squishy-scsi/squishy/docs/mascot.md

# Mascot - Sachi

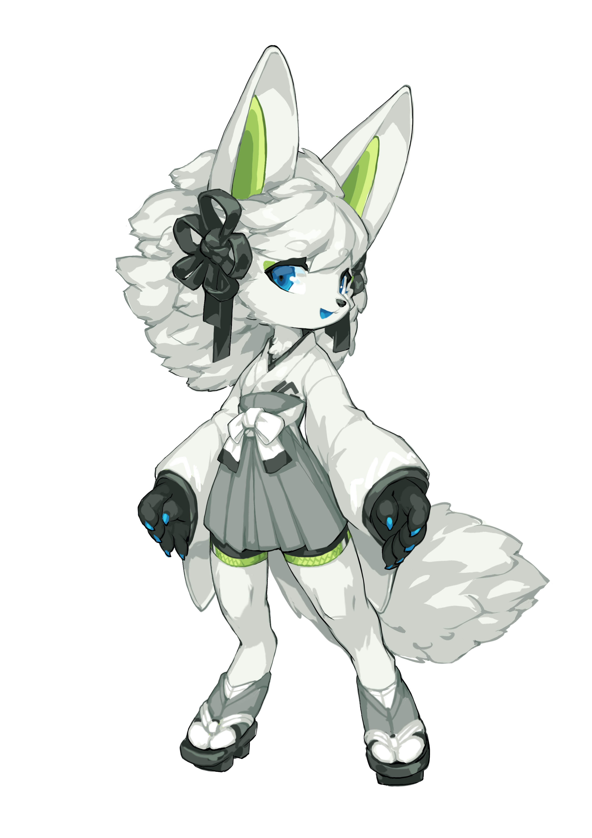
[picture p3: contrib/img/sachi/electrichearts_20211013A_sachi_trans.png]
```{image} ../contrib/img/sachi/electrichearts_20211013A_sachi_trans.png
```

## About

Sachi (さち, 幸, means happiness) is a spirit fox who attaches to an old magnetic tape drive. She loves to fiddle with old technology. Sachi used to be the divine agent of a small Shinto shrine called Suka Jinja (素華神社).

She was known for helping the locals with her wisdom in the past. Nowadays her shrine has been built over by a university, and she assumes her human identity as Professor Suka Sachiko (須賀 早智子) and teaches Japanese History and Computer Science there.

## Images

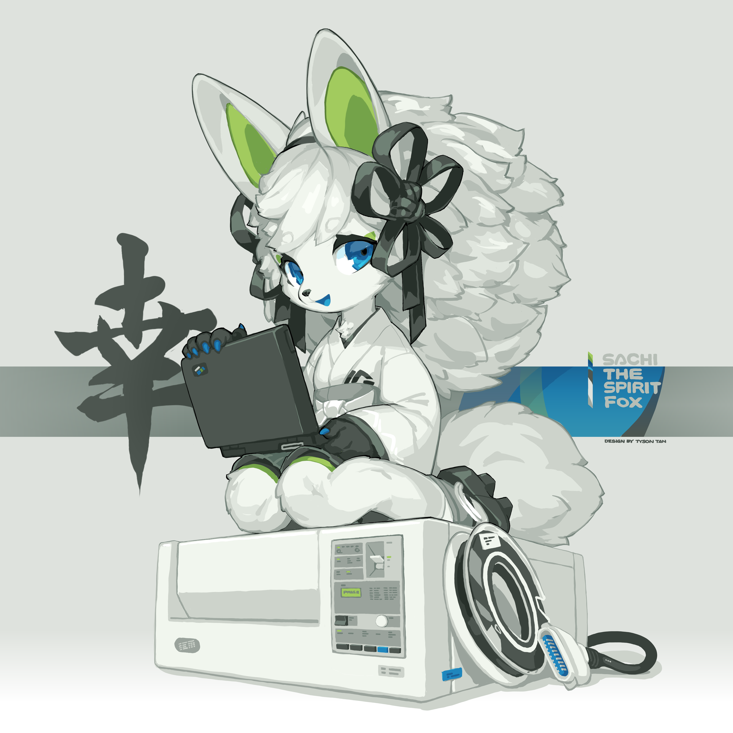
[picture p4: contrib/img/sachi/electrichearts_20220323A_sachi.png]
```{image} ../contrib/img/sachi/electrichearts_20220323A_sachi.png
```

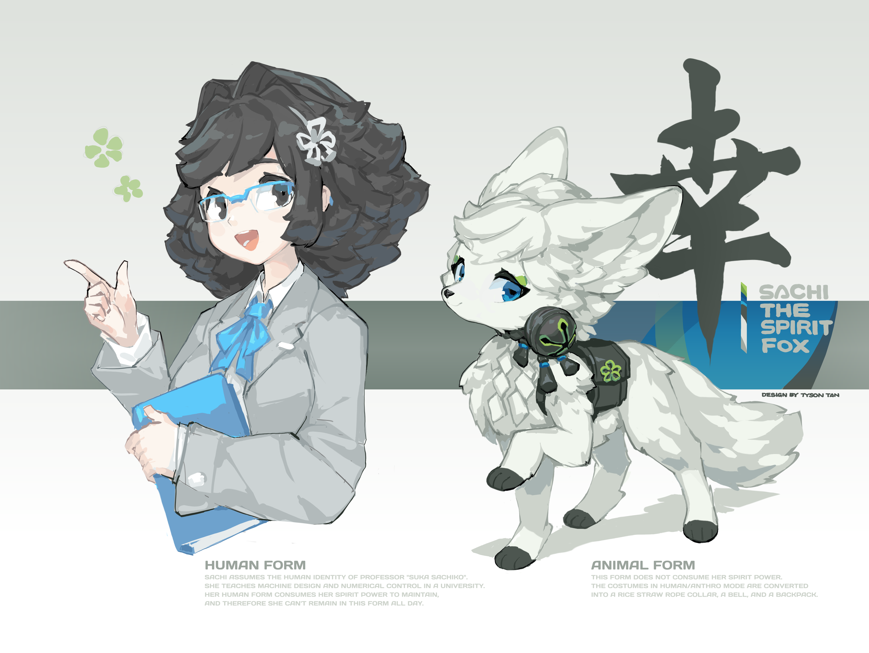
[picture p5: contrib/img/sachi/electrichearts_20230322A_sachi_human_english.png]
```{image} ../contrib/img/sachi/electrichearts_20230322A_sachi_human_english.png
```

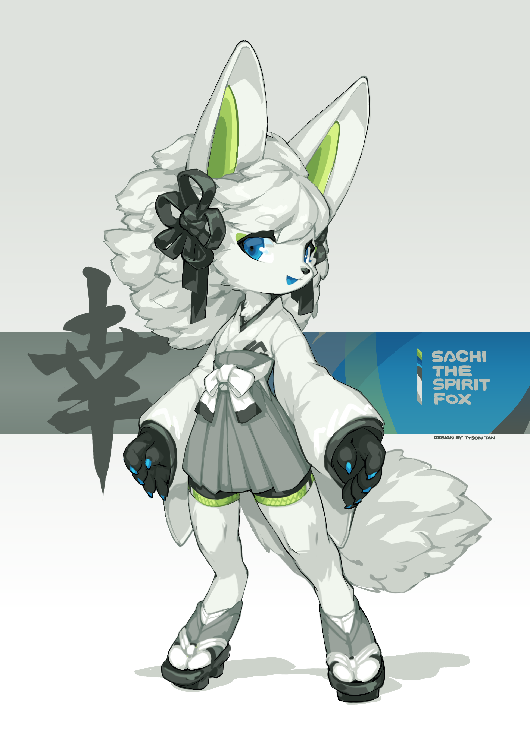
[picture p6: contrib/img/sachi/electrichearts_20211013A_sachi.png]
```{image} ../contrib/img/sachi/electrichearts_20211013A_sachi.png
```

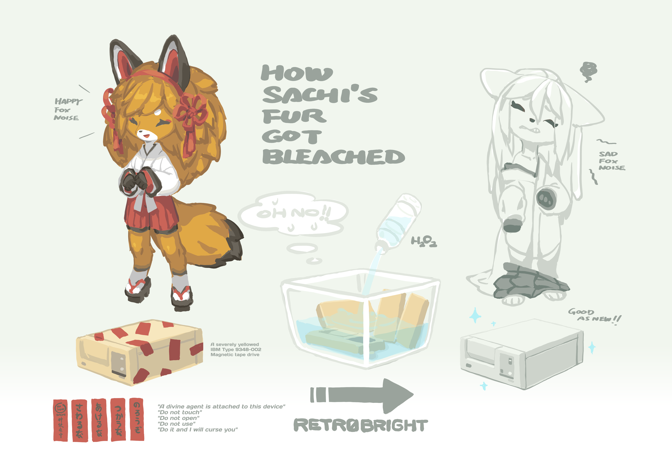
[picture p7: contrib/img/sachi/electrichearts_20220325A_sachi_yellow_english.png]
```{image} ../contrib/img/sachi/electrichearts_20220325A_sachi_yellow_english.png
```

Full-resolution images with and without transparent backgrounds can be downloaded from the [GitHub Repository] in the [`etc/img/sachi`] directory.

## License

Sachi was designed and illustrated by the amazing [Tyson Tan (tysontan.com)]. He provides mascot design service for free and open source software projects, free of charge, under free license.

She is dual-licensed under the [BSD-3-Clause] and the Creative Commons [CC-BY-SA]

The full text of the [BSD-3-Clause] can be found in the [LICENSE.software] file in the root of the repository

The full text of the Creative Commons [CC-BY-SA] can be found in the [LICENSE.docs] file in the root of the repository

[GitHub Repository]: https://github.com/squishy-scsi/squishy/tree/main/
[`etc/img/sachi`]: https://github.com/squishy-scsi/squishy/tree/main/contrib/img/sachi
[Tyson Tan (tysontan.com)]: https://tysontan.com
[BSD-3-Clause]: https://spdx.org/licenses/BSD-3-Clause.html
[LICENSE.software]: https://github.com/squishy-scsi/squishy/tree/main/LICENSE.software
[CC-BY-SA]: https://creativecommons.org/licenses/by-sa/2.0/
[LICENSE.docs]: https://github.com/squishy-scsi/squishy/tree/main/LICENSE.docs
