squishy-scsi/squishy/contrib/img/drive-harddisk-scsi.png

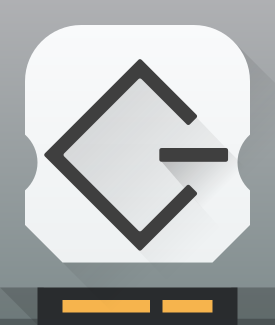
contrib/img/drive-harddisk-scsi.png
