squishy-scsi/squishy/contrib/img/sachi/doric-sachi.png

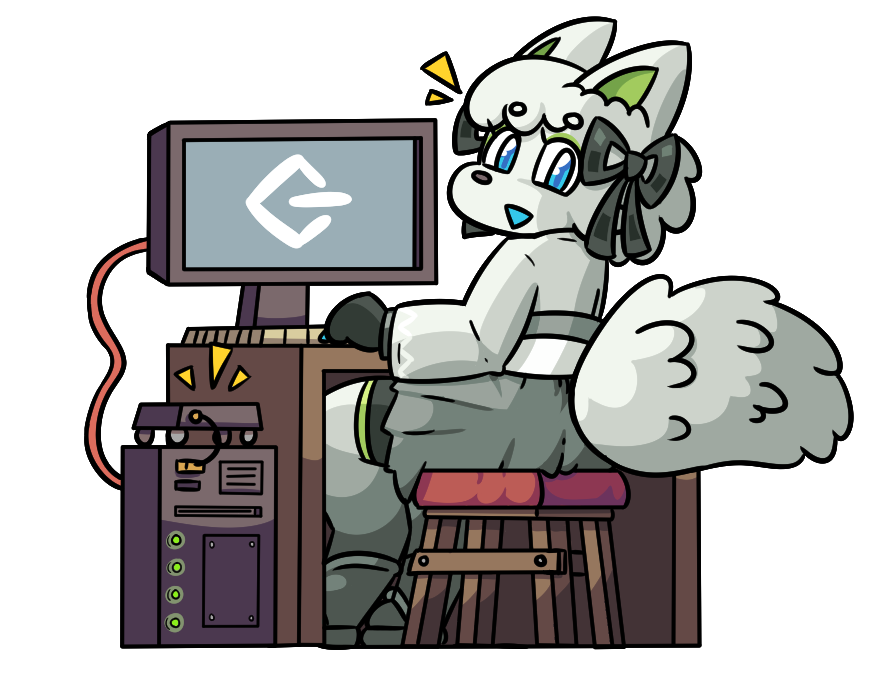
contrib/img/sachi/doric-sachi.png
