squishy-scsi/squishy/squishy/gateware/peripherals/hyperram.py

# SPDX-License-Identifier: BSD-3-Clause

'''

'''

from torii      import Elaboratable, Module
from ..platform import SquishyPlatformType


__all__ = (
	'HyperRAM',
)


class HyperRAM(Elaboratable):
	'''

	'''

	def __init__(self):
		pass

	def elaborate(self, platform: SquishyPlatformType | None) -> Module:
		m = Module()

		return m
