squishy-scsi/squishy/tests/gateware/peripherals/test_psram.py

# SPDX-License-Identifier: BSD-3-Clause
# torii: UnusedElaboratable=no

from os                                 import getenv
from random                             import randbytes

from torii                              import Elaboratable, Module, Signal, ClockDomain
from torii.lib.fifo                     import AsyncFIFO
from torii.sim                          import Settle
from torii.test                         import ToriiTestCase
from torii.test.mock                    import MockPlatform

from squishy.support.test               import SPIGatewareTest
from squishy.gateware.peripherals.spi   import SPIController, SPICPOL
from squishy.gateware.peripherals.psram import SPIPSRAM, SPIPSRAMCmd

if getenv('GITHUB_WORKSPACE') is not None:
	_PSRAM_DATA = randbytes(1536) # 1024 to get an addr wrap + a bit
else:
	_PSRAM_DATA = randbytes(4096) # :nocov:

clk  = Signal()
cs   = Signal()
copi = Signal()
cipo = Signal()

class DUTWrapper(Elaboratable):
	def __init__(self) -> None:

		self._write_fifo = AsyncFIFO(
			width = 8, depth = len(_PSRAM_DATA), r_domain = 'sync', w_domain = 'sync'
		)
		self._read_fifo  = AsyncFIFO(
			width = 8, depth = len(_PSRAM_DATA) // 2, r_domain = 'sync', w_domain = 'sync'
		)
		self._spi   = SPIController(
			clk = clk, cipo = cipo, copi = copi, cs = cs, cpol = SPICPOL.LOW
		)
		self._psram = SPIPSRAM(
			controller = self._spi, write_fifo = self._write_fifo, read_fifo = self._read_fifo
		)


		self.ready      = self._psram.ready
		self.done       = self._psram.done
		self.start_r    = self._psram.start_r
		self.start_w    = self._psram.start_w
		self.finish     = self._psram.finish
		self.rst_addrs  = self._psram.rst_addrs
		self.start_addr = self._psram.start_addr
		self.curr_addr  = self._psram.curr_addr
		self.byte_count = self._psram.byte_count

		self.itr = Signal(range(len(_PSRAM_DATA)))


	def elaborate(self, _) -> Module:
		m = Module()

		m.submodules.write_fifo = self._write_fifo
		m.submodules.read_fifo  = self._read_fifo
		m.submodules.spi   = self._spi
		m.submodules.psram = self._psram

		m.domains.test = ClockDomain()

		with m.If(self._write_fifo.w_en | self._read_fifo.w_en):
			m.d.sync += [ self.itr.inc(), ]

		return m


class SPIPSRAMTests(SPIGatewareTest):
	dut: DUTWrapper = DUTWrapper
	dut_args = { }
	domains = (('sync', 60e6), ('test', 60e6))
	platform = MockPlatform()

	def __init__(self, *args, **kwargs) -> None:
		super().__init__(*args, **kwargs)

	def fill_write_fifo(self, byte: int, idx: int):
		final   = idx == len(_PSRAM_DATA) - 1
		do_cont = (idx & 1023) != 1023

		yield self.dut._write_fifo.w_en.eq(1)
		yield self.dut._write_fifo.w_data.eq(byte)
		yield
		yield self.dut._write_fifo.w_en.eq(0)
		yield from self.step(3)

		yield from self.spi_trans(
			copi_data = (byte,), partial = not final, continuation = True
		)

		# We are wrapping addresses
		if not do_cont:
			yield Settle()
			self.assertEqual((yield cs), 0)
			yield

			if not final:
				yield from self.step(10)
				yield from self.settle()
				self.assertEqual((yield cs), 1)
				yield from self.step(10)
				self.assertEqual((yield cs), 1)
				yield from self.spi_trans(
					copi_data = (SPIPSRAMCmd.WRITE, *(idx + 1).to_bytes(3, byteorder = 'big')), partial = True, continuation = True
				)

	def spi_trans(self, *,
		copi_data: tuple[int, ...] | None = None, cipo_data: tuple[int, ...] | None = None, partial: bool = False, continuation: bool = False
	):
		if cipo_data is not None and copi_data is not None:
			self.assertEqual(len(cipo_data), len(copi_data))

		bytes = max(0 if copi_data is None else len(copi_data), 0 if cipo_data is None else len(cipo_data))
		self.assertEqual((yield clk), 0)
		if continuation:
			yield Settle()
			self.assertEqual((yield cs), 1)
		else:
			self.assertEqual((yield cs), 0)
			yield Settle()
		yield
		self.assertEqual((yield clk), 0)
		self.assertEqual((yield cs), 1)
		yield Settle()
		# yield
		for byte in range(bytes):
			for bit in range(8):
				if bit == 0:
					self.assertEqual((yield clk), 0)
				else:
					self.assertEqual((yield clk), 1)
				self.assertEqual((yield cs), 1)
				yield Settle()
				if cipo_data is not None and cipo_data[byte] is not None:
					yield cipo.eq(((cipo_data[byte] << bit) & 0x80) >> 7)
				yield
				self.assertEqual((yield clk), 0)
				self.assertEqual((yield cs), 1)
				if copi_data is not None and copi_data[byte] is not None:
					self.assertEqual((yield copi), ((copi_data[byte] << bit) & 0x80) >> 7)
				yield Settle()
				yield
			if byte < bytes - 1:
				self.assertEqual((yield clk), 1)
				self.assertEqual((yield cs), 1)
			self.assertEqual((yield self.dut.done), 0)
			yield Settle()
			if cipo_data is not None and cipo_data[byte] is not None:
				yield cipo.eq(0)
			if byte < bytes - 1:
				yield
		if not partial:
			self.assertEqual((yield clk), 0)
			self.assertEqual((yield cs), 0)
			yield Settle()
			yield


	@ToriiTestCase.simulation
	@ToriiTestCase.sync_domain(domain = 'sync')
	def test_psram_write(self):
		yield
		# Check to ensure SPI bus is idle
		self.assertEqual((yield clk),  0)
		self.assertEqual((yield cs),   0)
		self.assertEqual((yield copi), 0)
		self.assertEqual((yield cipo), 0)
		# Ensure the FSM is ready and willing
		self.assertEqual((yield self.dut.ready), 1)
		# Setup the PSRAM Address stuff
		yield self.dut._psram.start_addr.eq(0)
		yield self.dut.rst_addrs.eq(1)
		yield Settle()
		yield
		yield self.dut.rst_addrs.eq(0)
		yield Settle()
		yield
		# Ensure the FSM is /still/ ready and willing
		self.assertEqual((yield self.dut.ready), 1)
		# Start a write
		yield self.dut.start_w.eq(1)
		yield self.dut.byte_count.eq(len(_PSRAM_DATA))
		yield Settle()
		yield
		yield self.dut.start_w.eq(0)
		yield Settle()
		self.assertEqual((yield self.dut.curr_addr), 0)
		self.assertEqual((yield self.dut.start_addr), 0)
		self.assertEqual((yield cs), 0)
		# Check to make sure the FSM advanced out of IDLE
		self.assertEqual((yield self.dut.ready), 0)
		yield from self.settle()
		self.assertEqual((yield cs), 1)
		yield from self.step(11)
		self.assertEqual((yield cs), 1)
		yield from self.spi_trans(copi_data = (SPIPSRAMCmd.WRITE, 0x00, 0x00, 0x00), partial = True, continuation = True)
		self.assertEqual((yield self.dut._write_fifo.r_rdy), 0)
		yield
		yield Settle()
		self.assertEqual((yield cs), 1)
		self.assertEqual((yield clk), 0)
		self.assertEqual((yield self.dut._write_fifo.r_rdy), 0)
		self.assertEqual((yield cs), 1)
		self.assertEqual((yield clk), 0)
		yield
		yield Settle()
		self.assertEqual((yield self.dut._write_fifo.r_rdy), 0)
		self.assertEqual((yield cs), 1)
		self.assertEqual((yield clk), 0)

		for idx, byte in enumerate(_PSRAM_DATA):
			yield from self.fill_write_fifo(byte, idx)

		yield from self.wait_until_low(cs, timeout = 16)
		yield from self.step(10)

		self.assertEqual((yield self.dut.done), 1)
		# Check to ensure SPI bus is idle, again
		self.assertEqual((yield clk),  0)
		self.assertEqual((yield cs),   0)
		self.assertEqual((yield cipo), 0)
		# Set our transaction to be done
		yield self.dut.finish.eq(1)
		yield
		self.assertEqual((yield self.dut.done), 1)
		yield self.dut.finish.eq(0)
		yield Settle()
		yield
		self.assertEqual((yield self.dut.done), 0)
		# Make sure the FSM is back waiting
		self.assertEqual((yield self.dut.ready), 1)
		yield Settle()
		yield
		yield Settle()
		yield

	@ToriiTestCase.simulation
	def test_psram_read(self):
		@ToriiTestCase.sync_domain(domain = 'test')
		def drain_fifo(self: SPIPSRAMTests):
			yield from self.wait_until_low(self.dut._read_fifo.w_rdy)
			# Stall the drain for a bit to test that we stop driving the SPI bus if our read FIFO is full
			yield from self.step(256)
			# Drain the FIFO
			for byte in _PSRAM_DATA:
				yield from self.wait_until_high(self.dut._read_fifo.r_rdy)
				yield self.dut._read_fifo.r_en.eq(1)
				yield
				yield self.dut._read_fifo.r_en.eq(0)
				self.assertEqual((yield self.dut._read_fifo.r_data), byte)
				yield Settle()
			yield from self.wait_until_low(self.dut._read_fifo.w_level)
			yield


		@ToriiTestCase.sync_domain(domain = 'sync')
		def psram_read(self: SPIPSRAMTests):
			yield
			# Check to ensure SPI bus is idle
			self.assertEqual((yield clk),  0)
			self.assertEqual((yield cs),   0)
			self.assertEqual((yield copi), 0)
			self.assertEqual((yield cipo), 0)
			# Ensure the FSM is ready and willing
			self.assertEqual((yield self.dut.ready), 1)
			# Setup the PSRAM Address stuff
			yield self.dut._psram.start_addr.eq(0xA5A5A5)
			yield self.dut.rst_addrs.eq(1)
			yield Settle()
			yield
			yield self.dut.rst_addrs.eq(0)
			yield Settle()
			yield
			# Ensure the FSM is /still/ ready and willing
			self.assertEqual((yield self.dut.ready), 1)
			# Start a read
			yield self.dut.start_r.eq(1)
			yield self.dut.byte_count.eq(len(_PSRAM_DATA))
			yield Settle()
			yield
			yield self.dut.start_r.eq(0)
			yield Settle()
			self.assertEqual((yield self.dut.curr_addr), 0xA5A5A5)
			self.assertEqual((yield self.dut.start_addr), 0xA5A5A5)
			self.assertEqual((yield cs), 0)
			# Check to make sure the FSM advanced out of IDLE
			self.assertEqual((yield self.dut.ready), 0)
			yield from self.settle()
			self.assertEqual((yield cs), 1)
			yield from self.step(11)
			self.assertEqual((yield cs), 1)
			yield from self.spi_trans(copi_data = (SPIPSRAMCmd.READ, 0xA5, 0xA5, 0xA5), partial = True, continuation = True)

			for idx, byte in enumerate(_PSRAM_DATA):
				final   = idx == len(_PSRAM_DATA) - 1
				do_cont = (idx & 1023) != 1023

				if idx == 0:
					yield

				if (yield self.dut._read_fifo.w_rdy) == 0:
					yield from self.wait_until_high(self.dut._read_fifo.w_rdy)
					yield

				yield from self.spi_trans(cipo_data = (byte,) , partial = do_cont, continuation = True)

				# We are wrapping addresses
				if not do_cont:
					if not final:
						yield from self.step(10)
						yield from self.settle()
						self.assertEqual((yield cs), 1)
						yield from self.step(10)
						self.assertEqual((yield cs), 1)
						yield from self.spi_trans(
							copi_data = (SPIPSRAMCmd.READ, *(idx + 0xA5A5A6).to_bytes(3, byteorder = 'big')), partial = True,
							continuation = True
						)
						yield

			yield from self.wait_until_low(cs, timeout = 16)
			yield from self.step(11)

			self.assertEqual((yield self.dut.done), 1)
			# Check to ensure SPI bus is idle, again
			self.assertEqual((yield clk),  0)
			self.assertEqual((yield cs),   0)
			self.assertEqual((yield copi), 0)
			# Set our transaction to be done
			yield self.dut.finish.eq(1)
			yield
			self.assertEqual((yield self.dut.done), 1)
			yield self.dut.finish.eq(0)
			yield Settle()
			yield
			self.assertEqual((yield self.dut.done), 0)
			# Make sure the FSM is back waiting
			self.assertEqual((yield self.dut.ready), 1)
			yield Settle()
			yield
			yield Settle()
			yield

		drain_fifo(self)
		psram_read(self)

	def test_psram_fifo_configurations(self):
		from torii.hdl.ir import Fragment

		spi = SPIController(
			clk = clk, cipo = cipo, copi = copi, cs = cs, cpol = SPICPOL.LOW
		)

		fifo = AsyncFIFO(
			width = 8, depth = len(_PSRAM_DATA), r_domain = 'sync', w_domain = 'sync'
		)

		# Make sure we dont accept a bogus config
		with self.assertRaisesRegex(
			ValueError, r'^One or both of `write_fifo` or `read_fifo` is required to be set$'
		):
			_ = SPIPSRAM(controller = spi)


		# Ensure we can construct a write-only SPIPSRAM controller
		dut = SPIPSRAM(controller = spi, write_fifo = fifo)

		self.assertIsNone(dut._read_fifo)
		self.assertIsNotNone(dut._write_fifo)
		self.assertTrue(hasattr(dut, 'start_w'))
		self.assertFalse(hasattr(dut, 'start_r'))
		m = dut.elaborate(None)
		self.assertIsNotNone(m)
		self.assertIsNotNone(Fragment.get(m, None))

		# Ensure we can construct a read-only SPIPSRAM controller
		dut = SPIPSRAM(controller = spi, read_fifo = fifo)

		self.assertIsNotNone(dut._read_fifo)
		self.assertIsNone(dut._write_fifo)
		self.assertFalse(hasattr(dut, 'start_w'))
		self.assertTrue(hasattr(dut, 'start_r'))
		m = dut.elaborate(None)
		self.assertIsNotNone(m)
		self.assertIsNotNone(Fragment.get(m, None))
